botletics/SIM7000-LTE-Shield/Media/Adafruit IO Command Feed.PNG

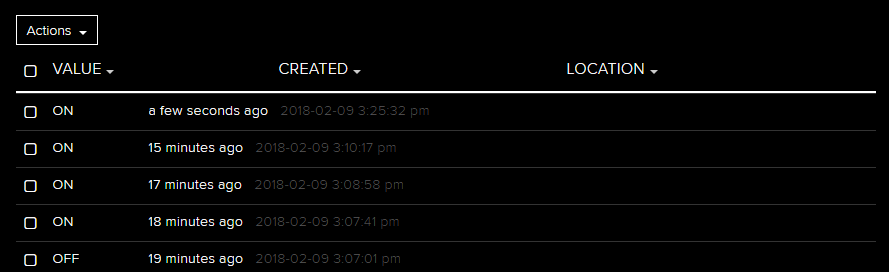
Media/Adafruit IO Command Feed.PNG
