botletics/SIM7000-LTE-Shield/Media/Adafruit IO Feeds.PNG

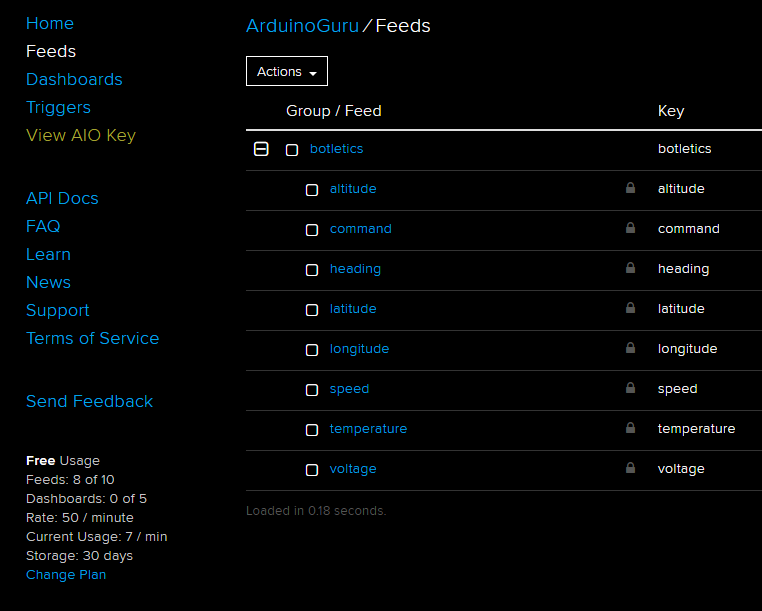
Media/Adafruit IO Feeds.PNG
