botletics/SIM7000-LTE-Shield/Media/AIO MQTT Command Message.PNG

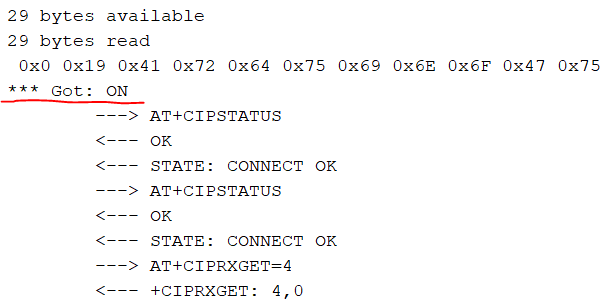
Media/AIO MQTT Command Message.PNG
