botletics/SIM7000-LTE-Shield/Media/Antenna Back.jpg

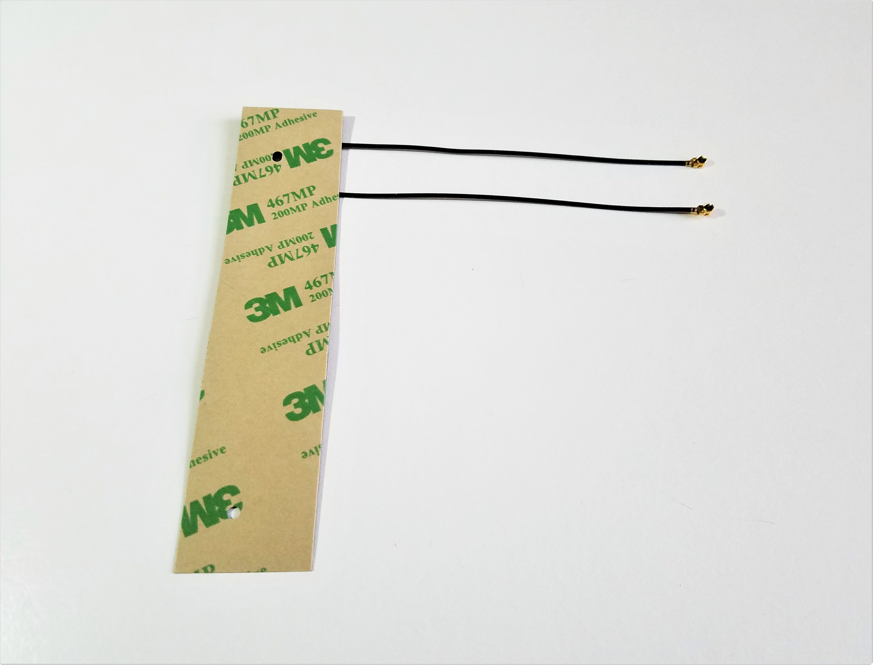
Media/Antenna Back.jpg
