botletics/SIM7000-LTE-Shield/Media/Antenna Front.jpg

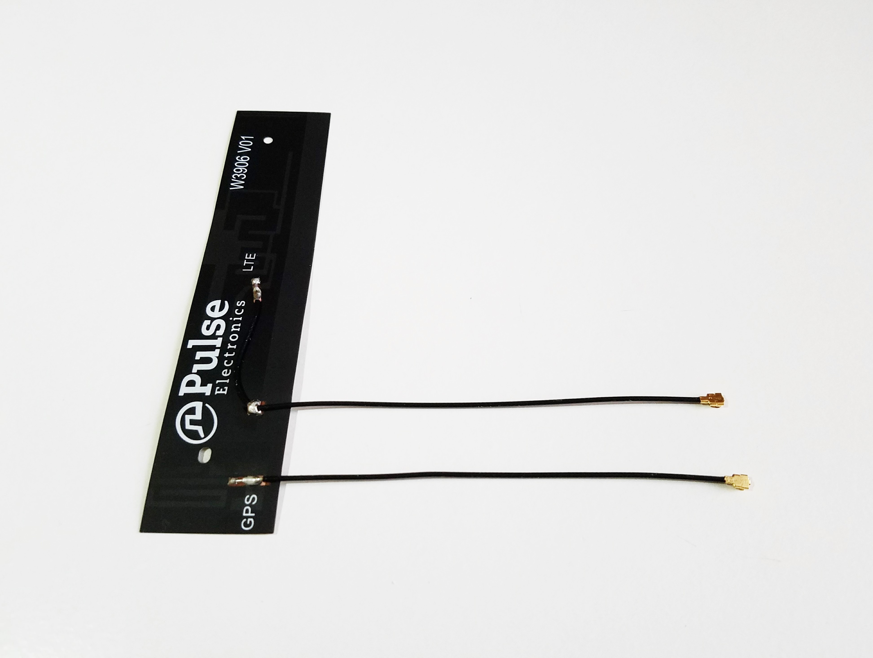
Media/Antenna Front.jpg
