botletics/SIM7000-LTE-Shield/Media/Arduino IDE Boards Screenshot.png

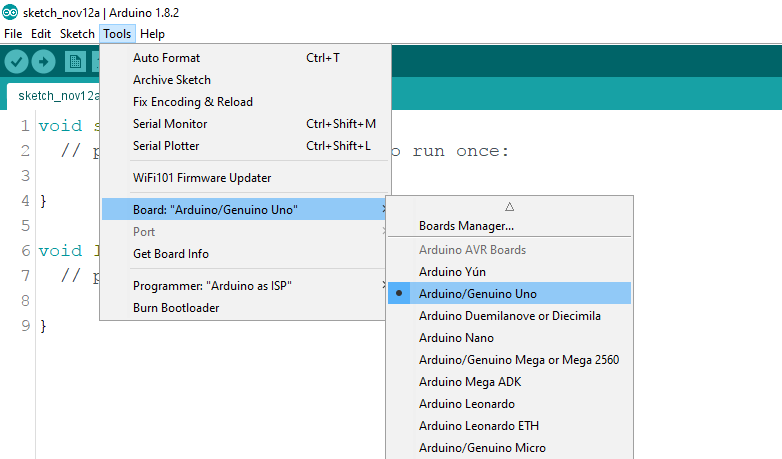
Media/Arduino IDE Boards Screenshot.png
