botletics/SIM7000-LTE-Shield/Media/Arduino IDE Example Screenshot.png

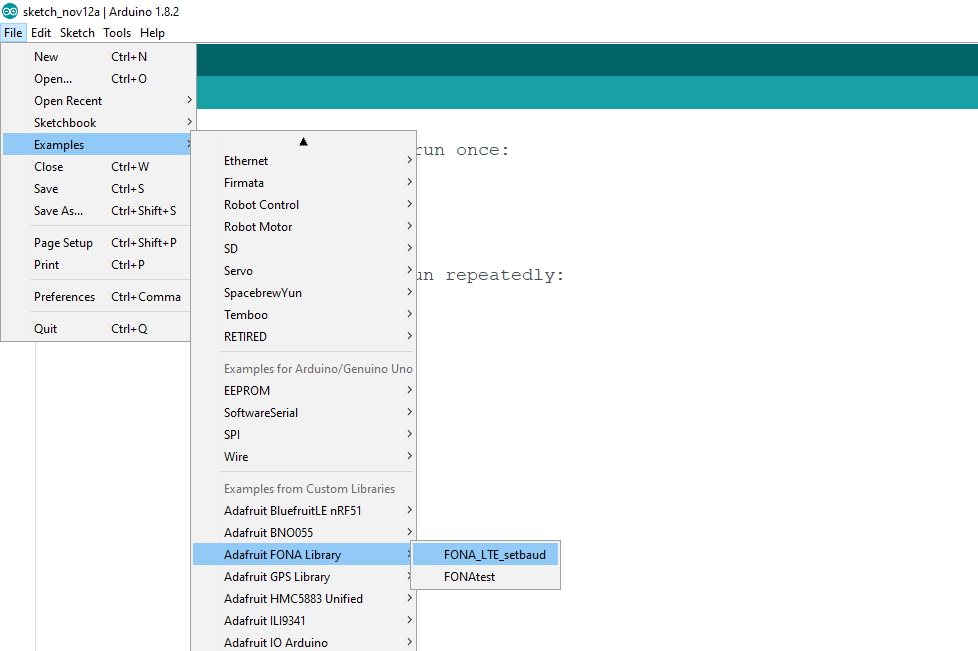
Media/Arduino IDE Example Screenshot.png
