botletics/SIM7000-LTE-Shield/Media/CAT-M_NB_Operator Map.jpg

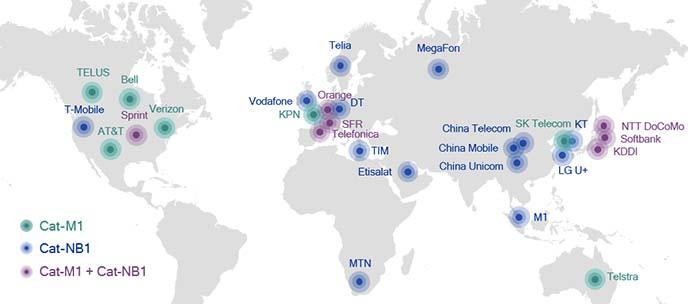
Media/CAT-M_NB_Operator Map.jpg
