botletics/SIM7000-LTE-Shield/Media/CloudMQTT Details Page.PNG

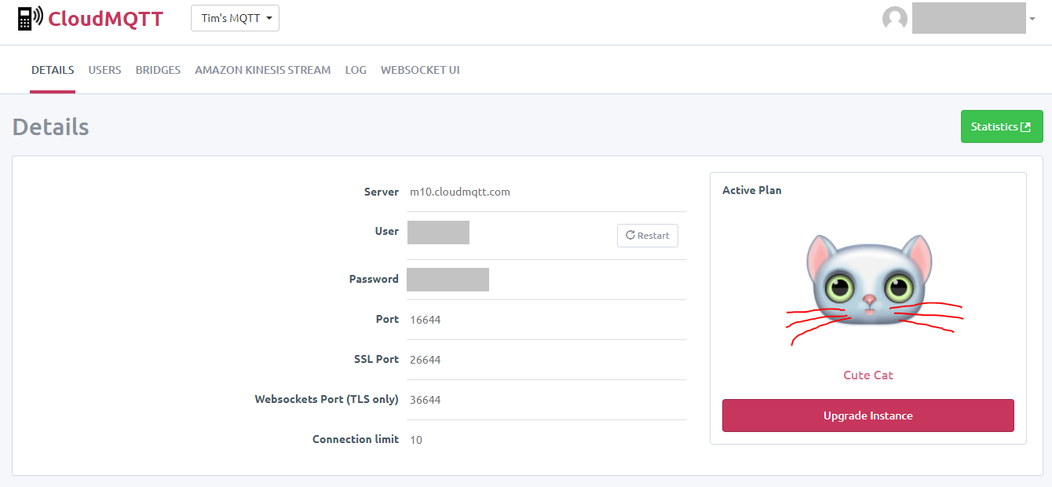
Media/CloudMQTT Details Page.PNG
