botletics/SIM7000-LTE-Shield/Media/CloudMQTT Websocket UI.PNG

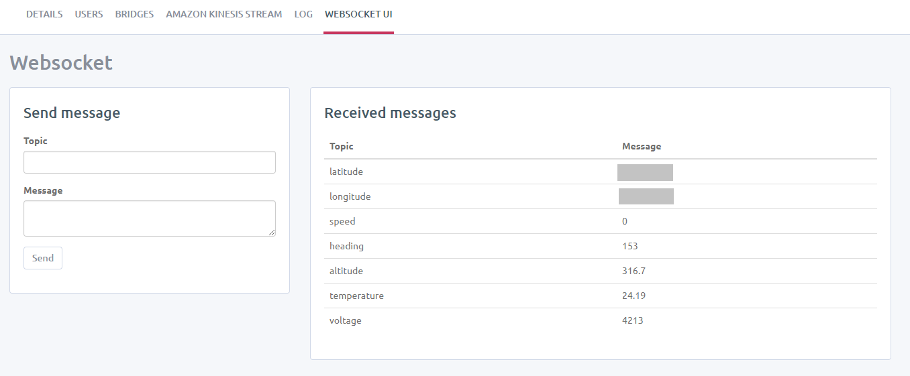
Media/CloudMQTT Websocket UI.PNG
