botletics/SIM7000-LTE-Shield/Media/Disable GPS.JPG

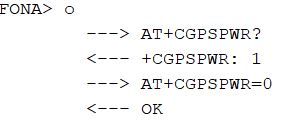
Media/Disable GPS.JPG
