botletics/SIM7000-LTE-Shield/Media/DONE LED Closeup v6.jpg

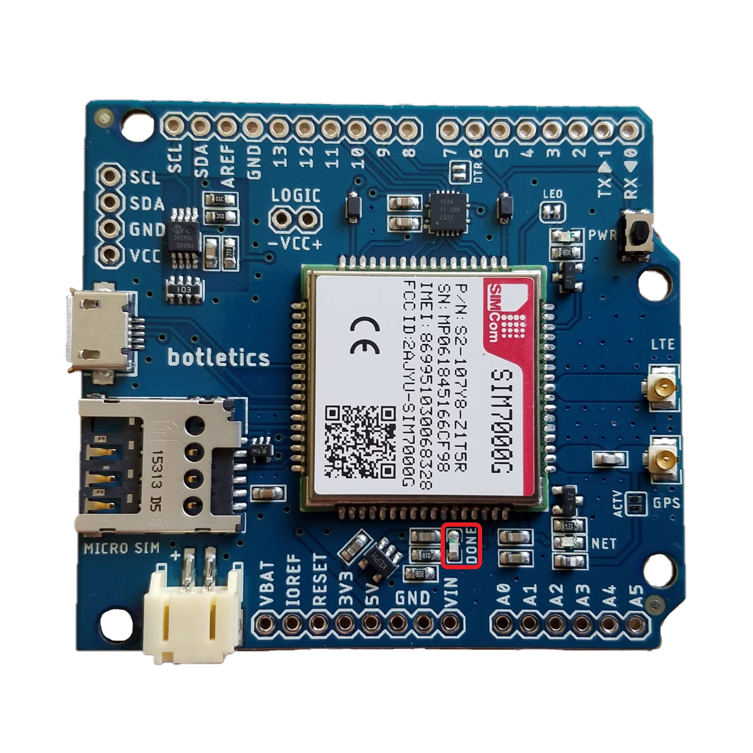
Media/DONE LED Closeup v6.jpg
