botletics/SIM7000-LTE-Shield/Media/Driver Update Remaining Updates.png

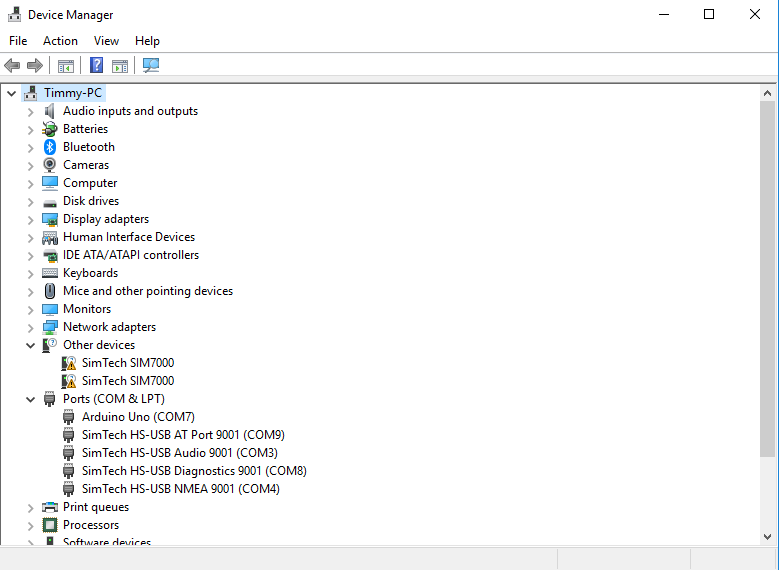
Media/Driver Update Remaining Updates.png
