botletics/SIM7000-LTE-Shield/Media/Driver Update Success COM Port.png

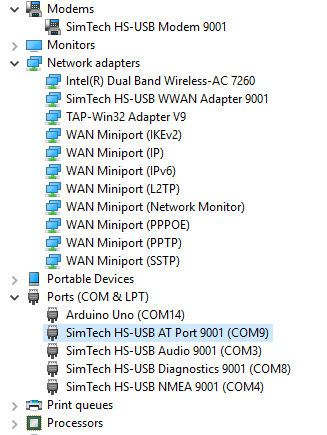
Media/Driver Update Success COM Port.png
