botletics/SIM7000-LTE-Shield/Media/Driver Update Success.png

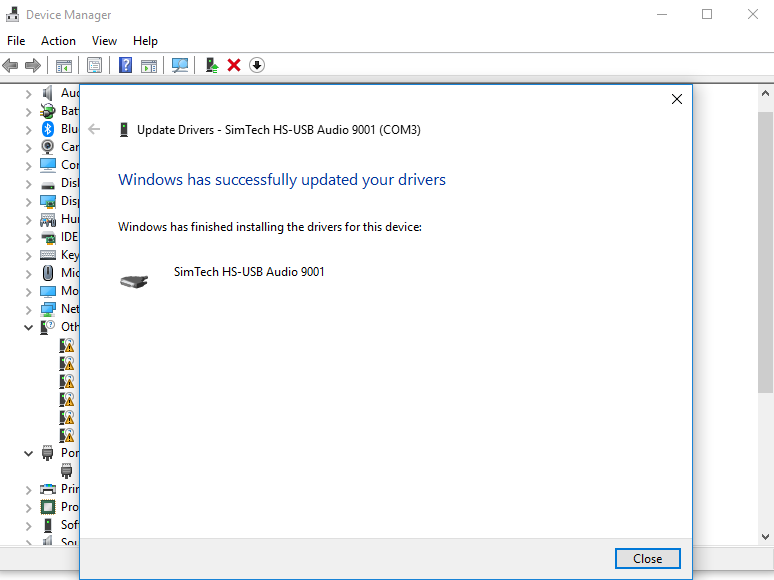
Media/Driver Update Success.png
