botletics/SIM7000-LTE-Shield/Media/Enable GPRS LTE.JPG

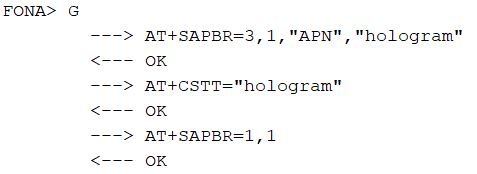
Media/Enable GPRS LTE.JPG
