botletics/SIM7000-LTE-Shield/Media/Enable GPRS.JPG

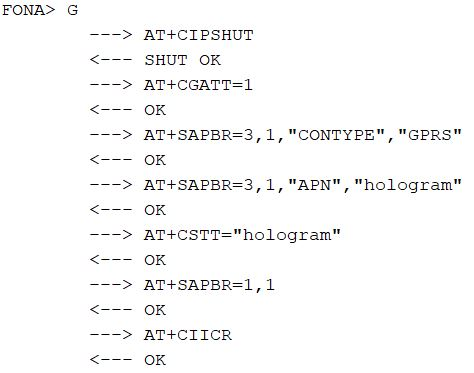
Media/Enable GPRS.JPG
