botletics/SIM7000-LTE-Shield/Media/Enable GPS.JPG

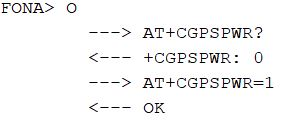
Media/Enable GPS.JPG
