botletics/SIM7000-LTE-Shield/Media/Folder Screenshot 1.png

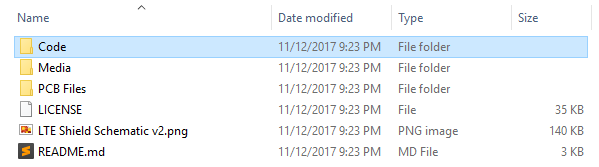
Media/Folder Screenshot 1.png
