botletics/SIM7000-LTE-Shield/Media/Folder Screenshot 2.png

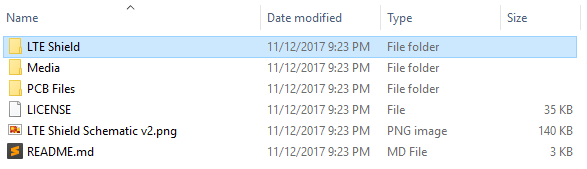
Media/Folder Screenshot 2.png
