botletics/SIM7000-LTE-Shield/Media/FONAtest Batt Example.PNG

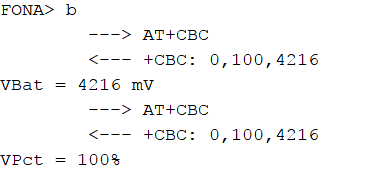
Media/FONAtest Batt Example.PNG
