botletics/SIM7000-LTE-Shield/Media/Github Download ZIP.png

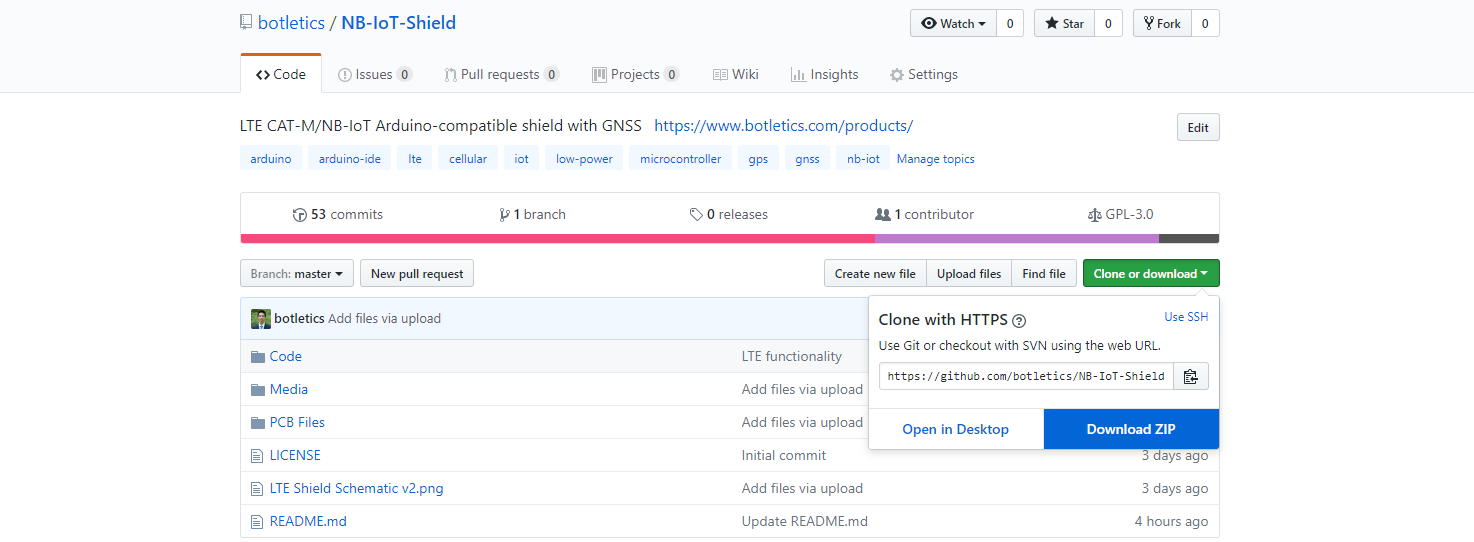
Media/Github Download ZIP.png
