botletics/SIM7000-LTE-Shield/Media/Hologram Console Data.PNG

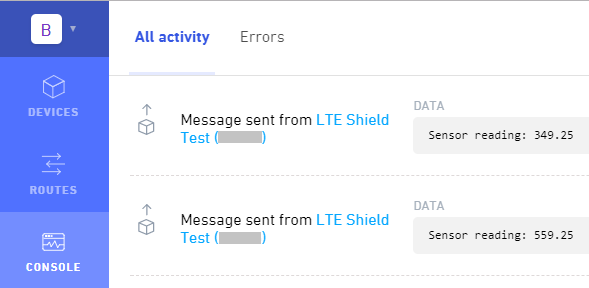
Media/Hologram Console Data.PNG
