botletics/SIM7000-LTE-Shield/Media/Hologram Device Screen.png

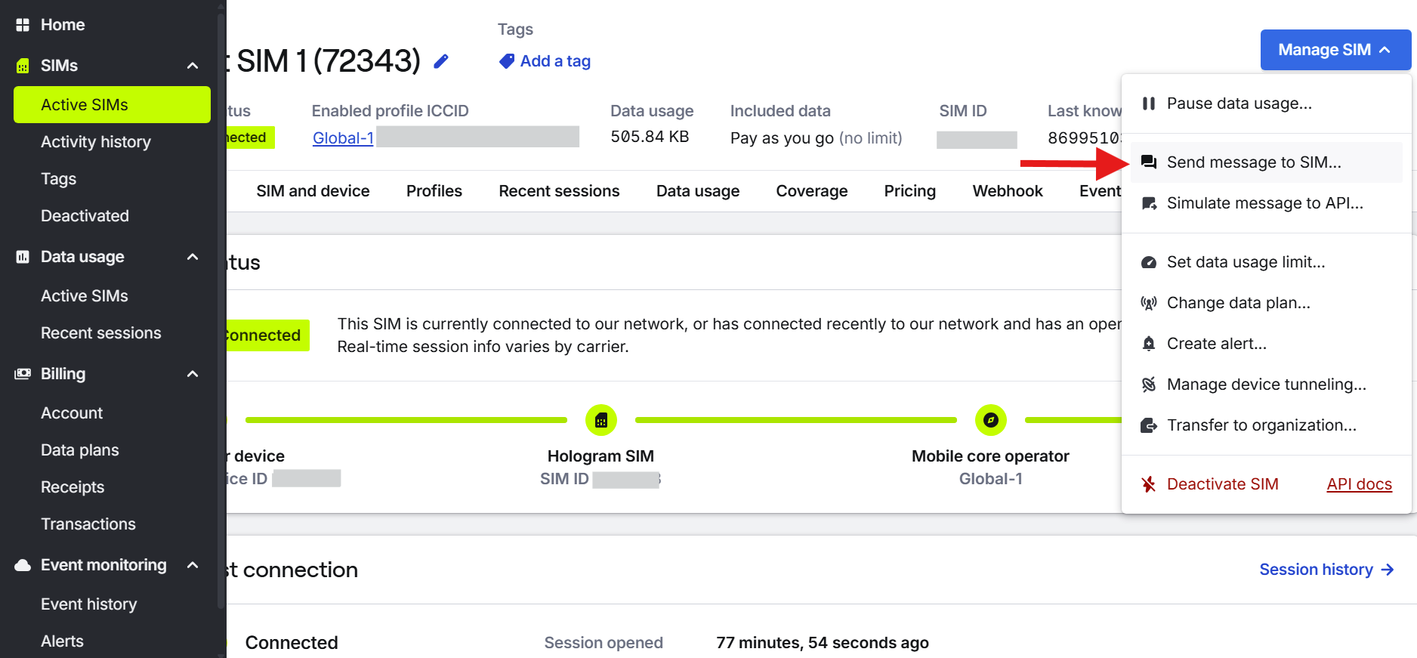
Media/Hologram Device Screen.png
