botletics/SIM7000-LTE-Shield/Media/Hologram Route Email Example.PNG

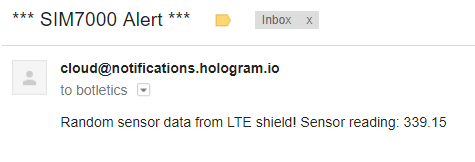
Media/Hologram Route Email Example.PNG
