botletics/SIM7000-LTE-Shield/Media/Hologram Route Email Fields.PNG

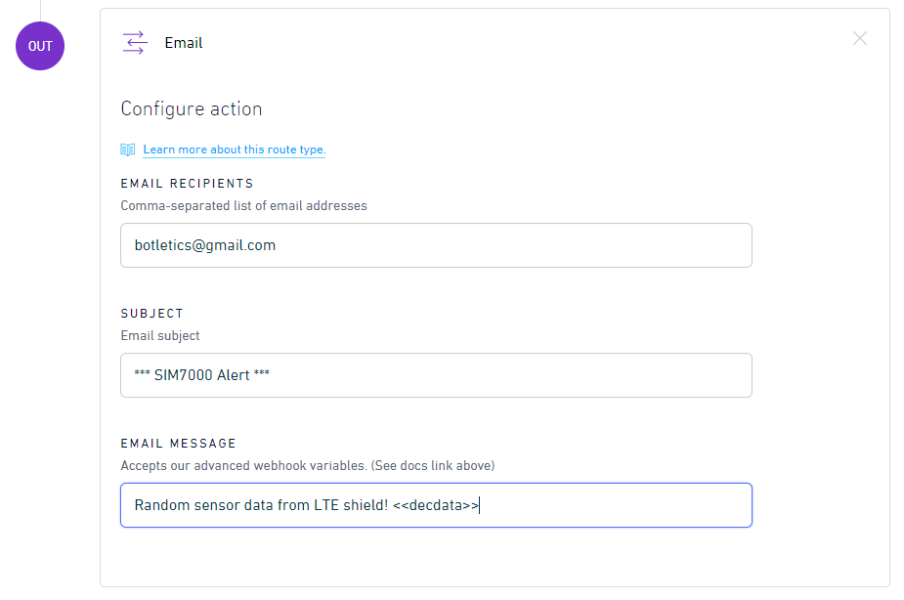
Media/Hologram Route Email Fields.PNG
