botletics/SIM7000-LTE-Shield/Media/Hologram Route SMS Action.PNG

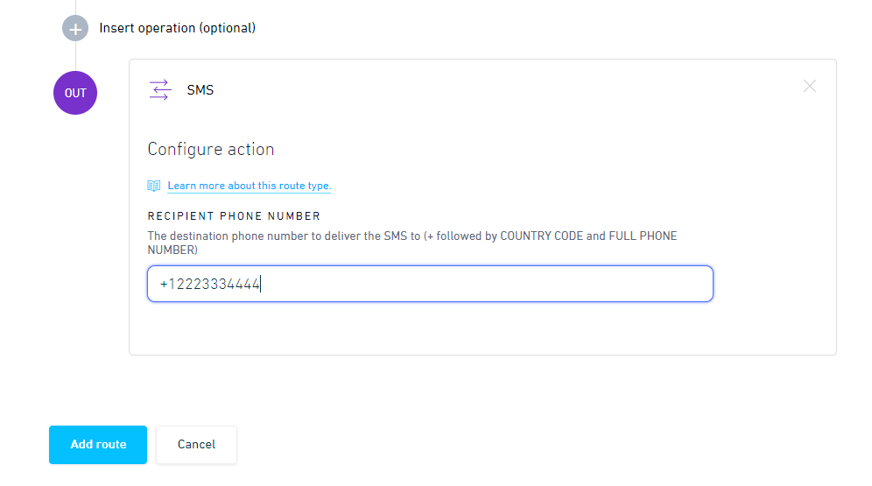
Media/Hologram Route SMS Action.PNG
