botletics/SIM7000-LTE-Shield/Media/Hologram Route SMS Topic.PNG

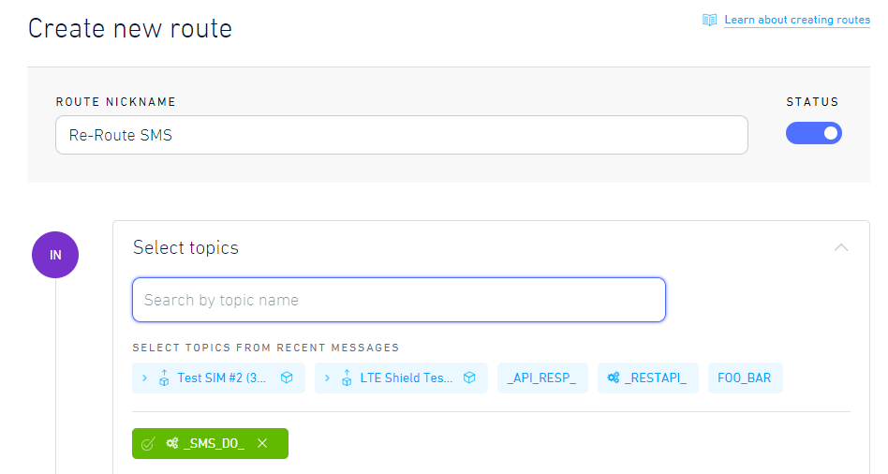
Media/Hologram Route SMS Topic.PNG
