botletics/SIM7000-LTE-Shield/Media/IoT Example GET Request.PNG

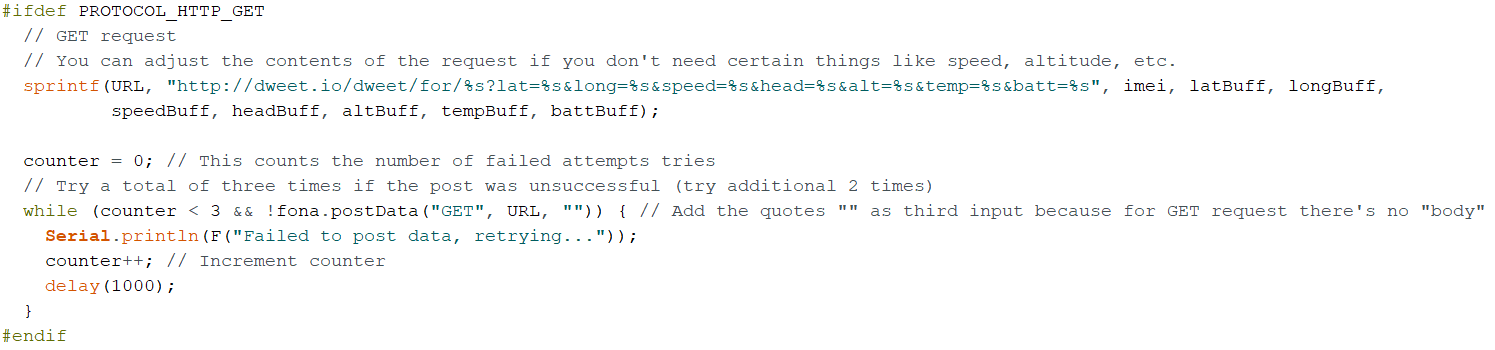
Media/IoT Example GET Request.PNG
