botletics/SIM7000-LTE-Shield/Media/IoT Example MQTT Publish Feeds.PNG

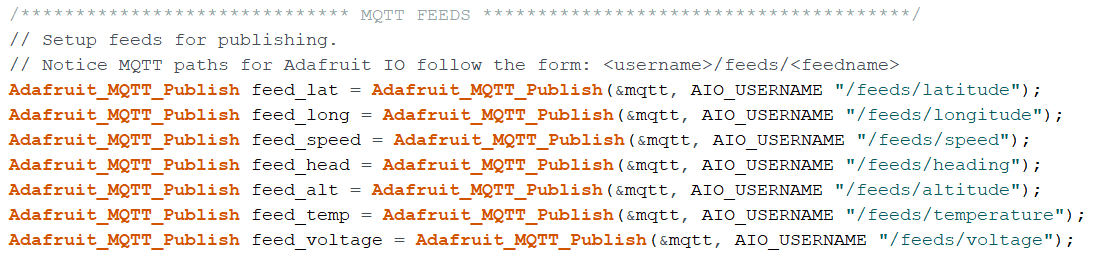
Media/IoT Example MQTT Publish Feeds.PNG
