botletics/SIM7000-LTE-Shield/Media/IoT Example POST Request.PNG

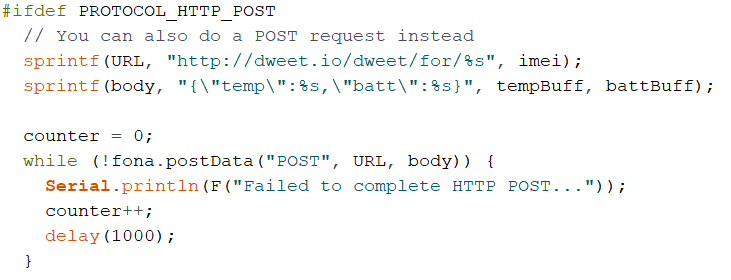
Media/IoT Example POST Request.PNG
