botletics/SIM7000-LTE-Shield/Media/IoT Example Sampling Rate.PNG

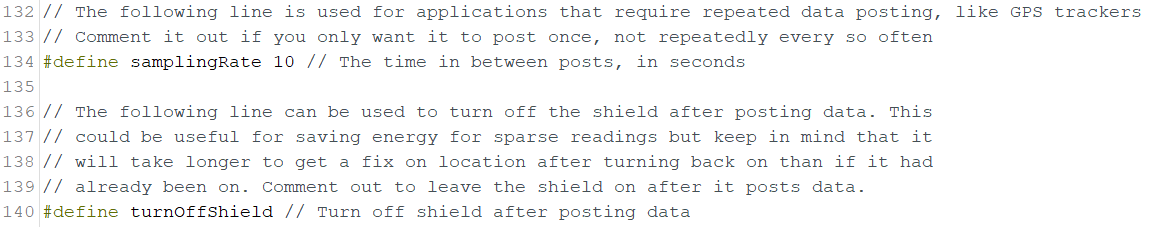
Media/IoT Example Sampling Rate.PNG
