botletics/SIM7000-LTE-Shield/Media/ITU Regions.png

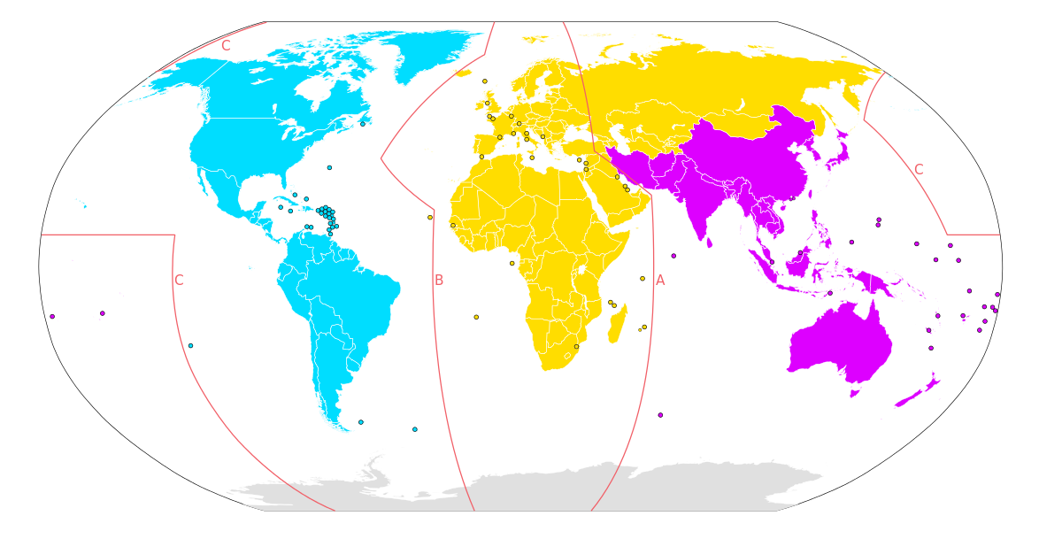
Media/ITU Regions.png
