botletics/SIM7000-LTE-Shield/Media/JST Connector Closeup v6.jpg

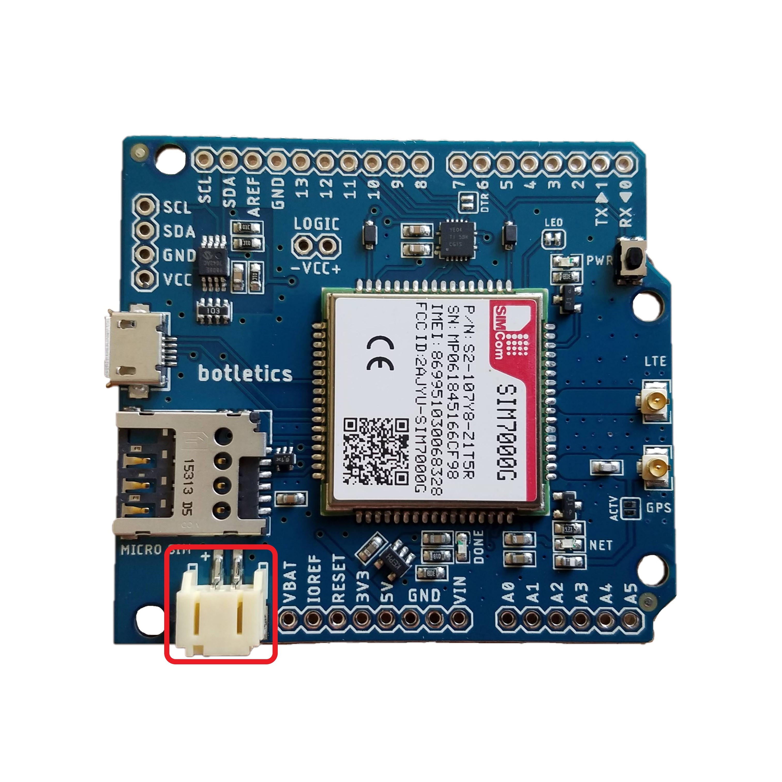
Media/JST Connector Closeup v6.jpg
