botletics/SIM7000-LTE-Shield/Media/Logic Voltage Selection Jumper.PNG

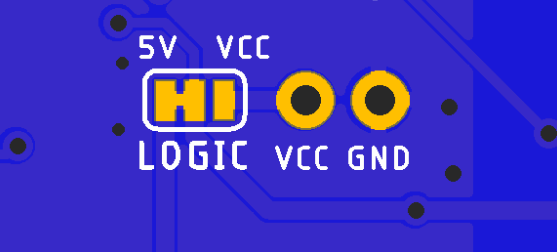
Media/Logic Voltage Selection Jumper.PNG
