botletics/SIM7000-LTE-Shield/Media/LTE Bands.JPG

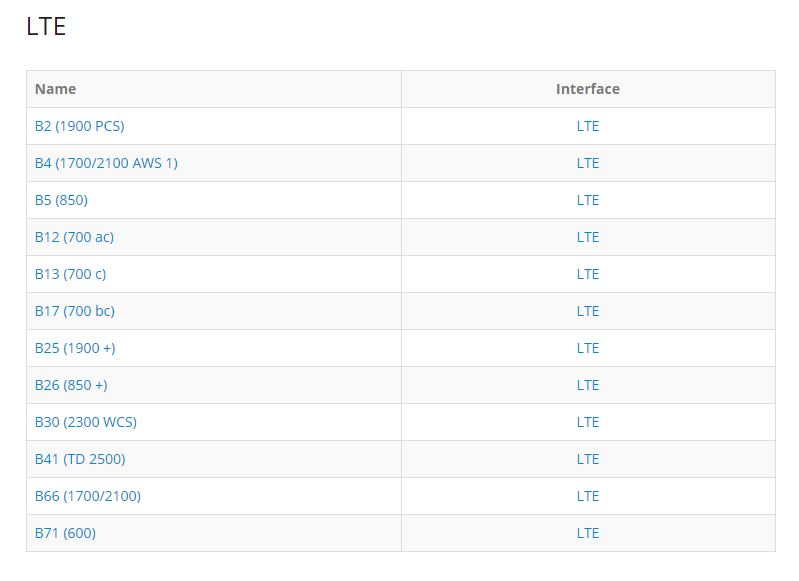
Media/LTE Bands.JPG
