botletics/SIM7000-LTE-Shield/Media/MCP9098 Demo.PNG

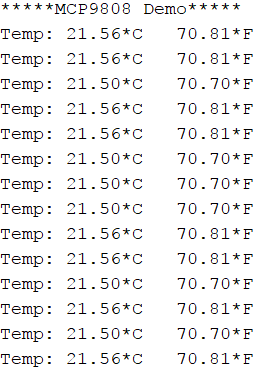
Media/MCP9098 Demo.PNG
