botletics/SIM7000-LTE-Shield/Media/MCP9808 Example Screenshot.png

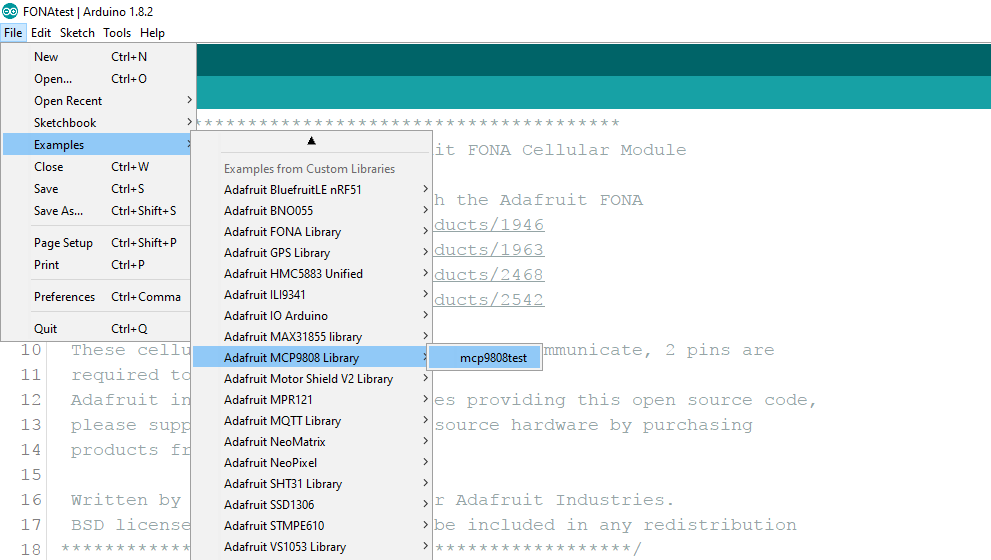
Media/MCP9808 Example Screenshot.png
