botletics/SIM7000-LTE-Shield/Media/Open Sesame from Hologram.png

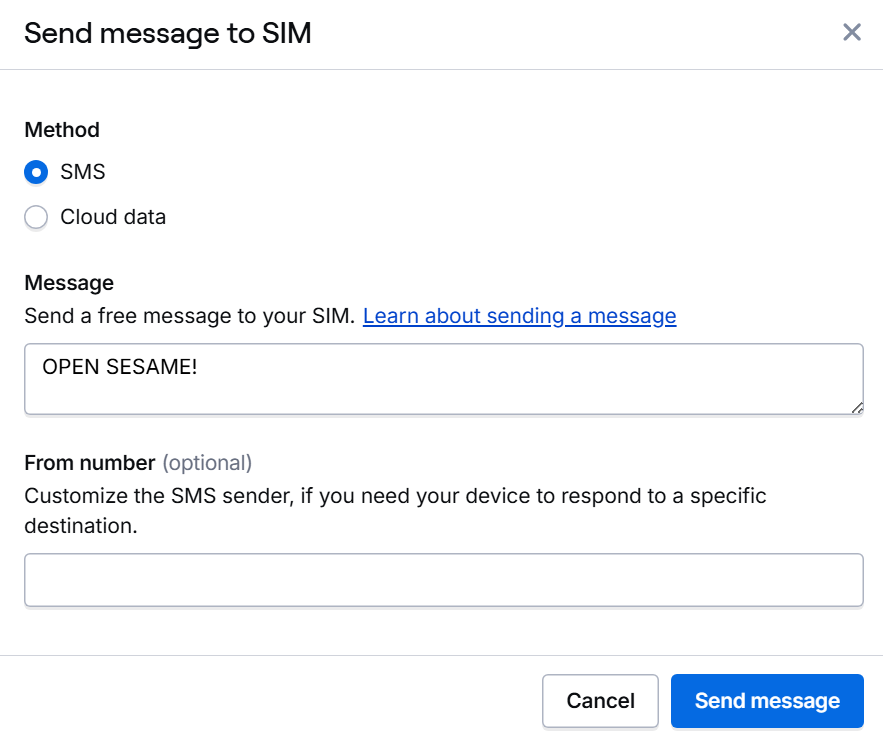
Media/Open Sesame from Hologram.png
