botletics/SIM7000-LTE-Shield/Media/QDL Tool Windows Compatibility Prompt.PNG

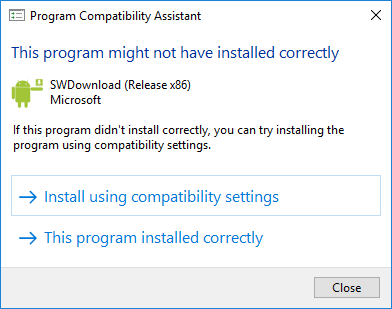
Media/QDL Tool Windows Compatibility Prompt.PNG
