botletics/SIM7000-LTE-Shield/Media/Read Dweet.JPG

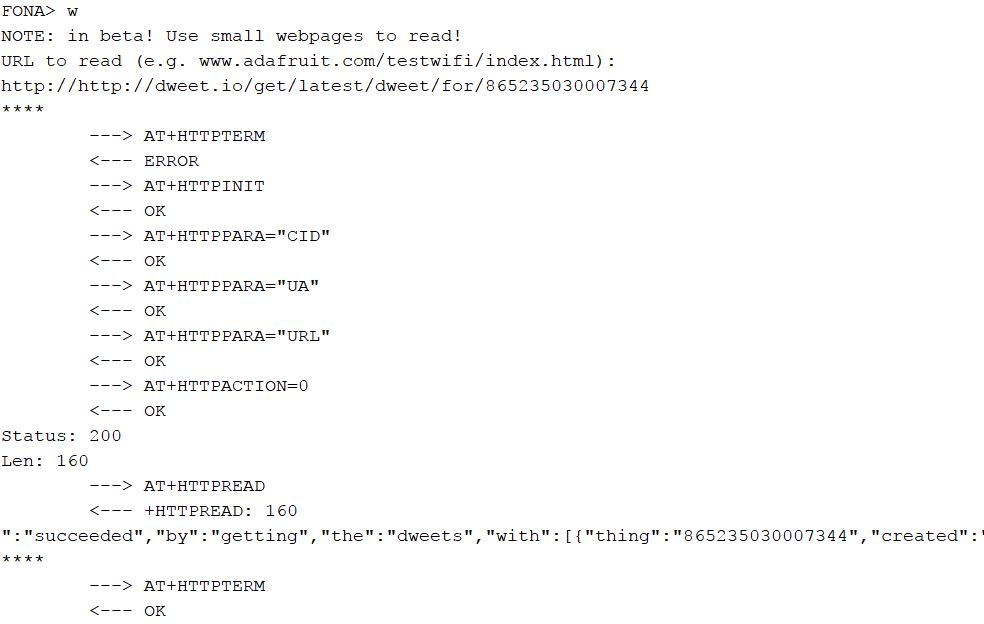
Media/Read Dweet.JPG
