botletics/SIM7000-LTE-Shield/Media/Read Webpage.JPG

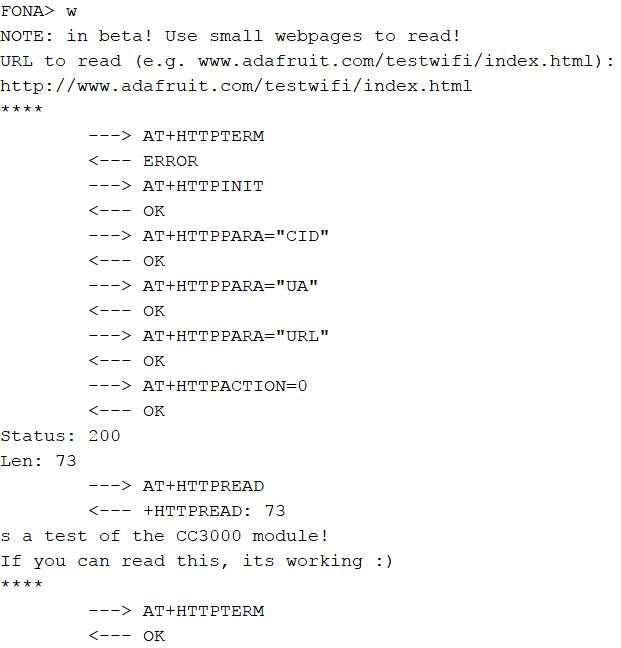
Media/Read Webpage.JPG
