botletics/SIM7000-LTE-Shield/Media/Send SMS from Hologram 1.png

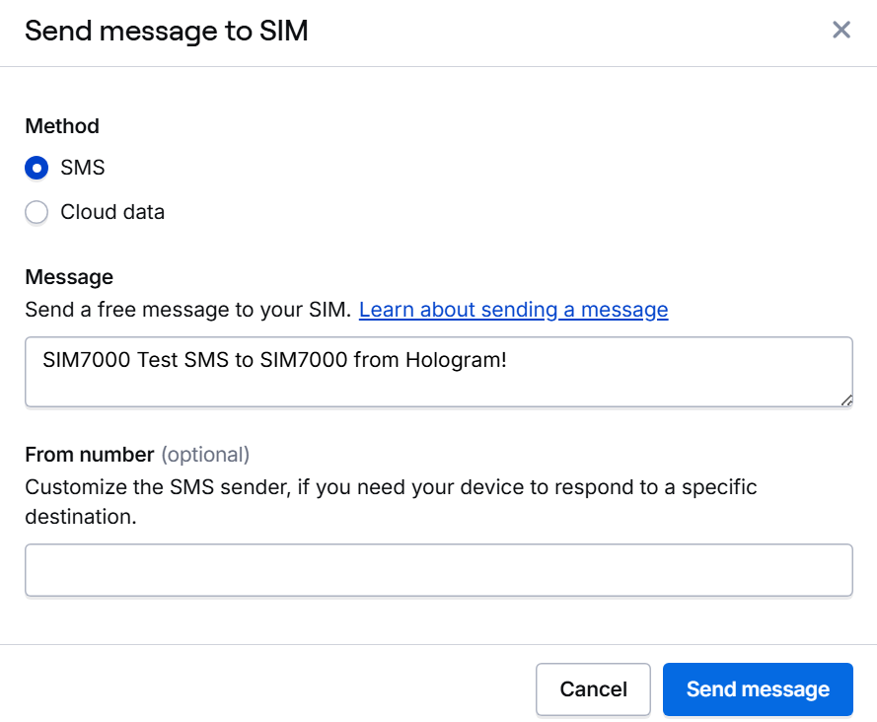
Media/Send SMS from Hologram 1.png
