botletics/SIM7000-LTE-Shield/Media/Send SMS from Hologram.png

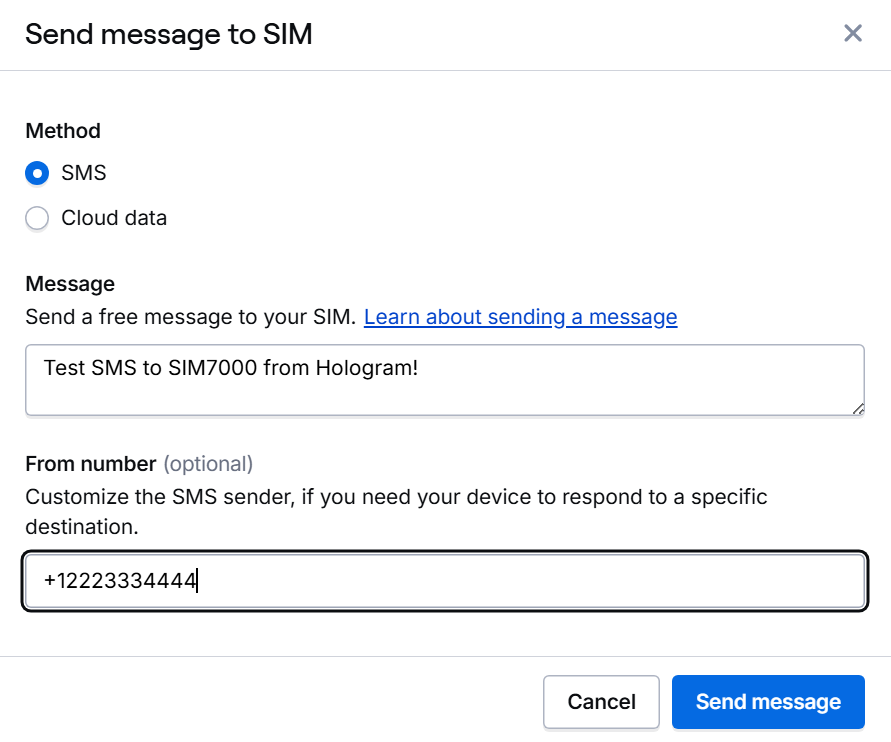
Media/Send SMS from Hologram.png
