botletics/SIM7000-LTE-Shield/Media/Send SMS.png

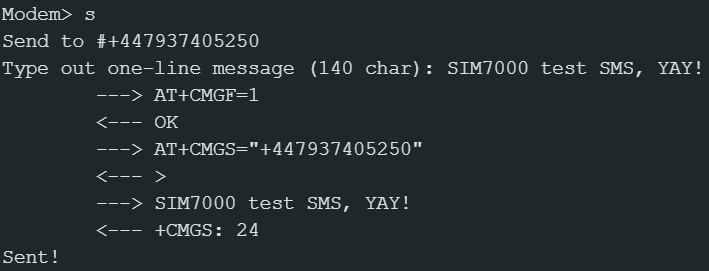
Media/Send SMS.png
