botletics/SIM7000-LTE-Shield/Media/Send to Dweet.JPG

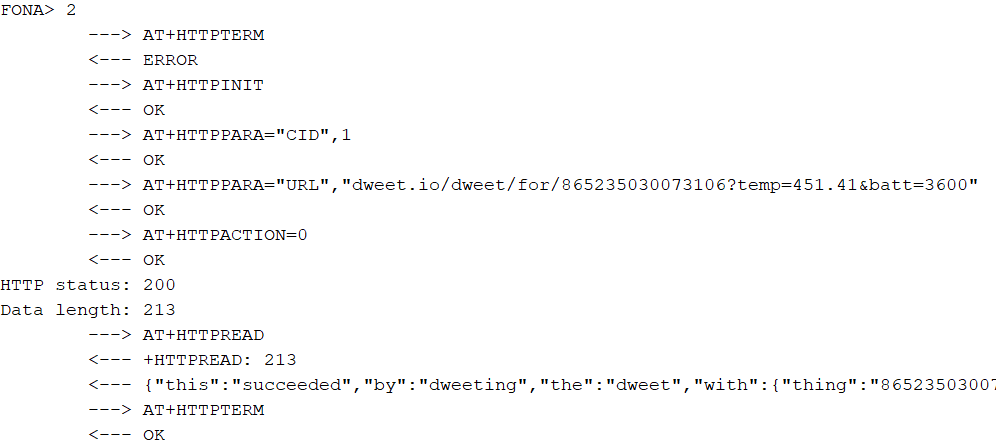
Media/Send to Dweet.JPG
