botletics/SIM7000-LTE-Shield/Media/SIM7000 Drivers Device Manager.JPG

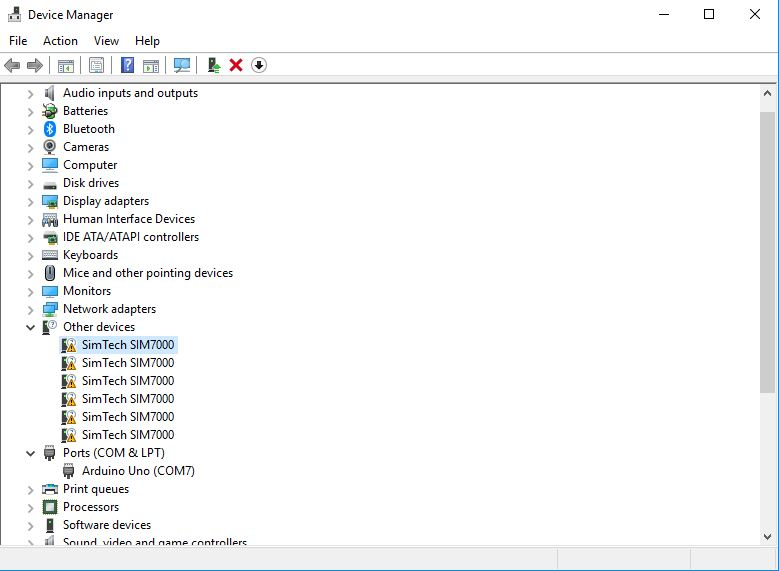
Media/SIM7000 Drivers Device Manager.JPG
