botletics/SIM7000-LTE-Shield/Media/SIM7000 LTE_Demo Serial Monitor 1.PNG

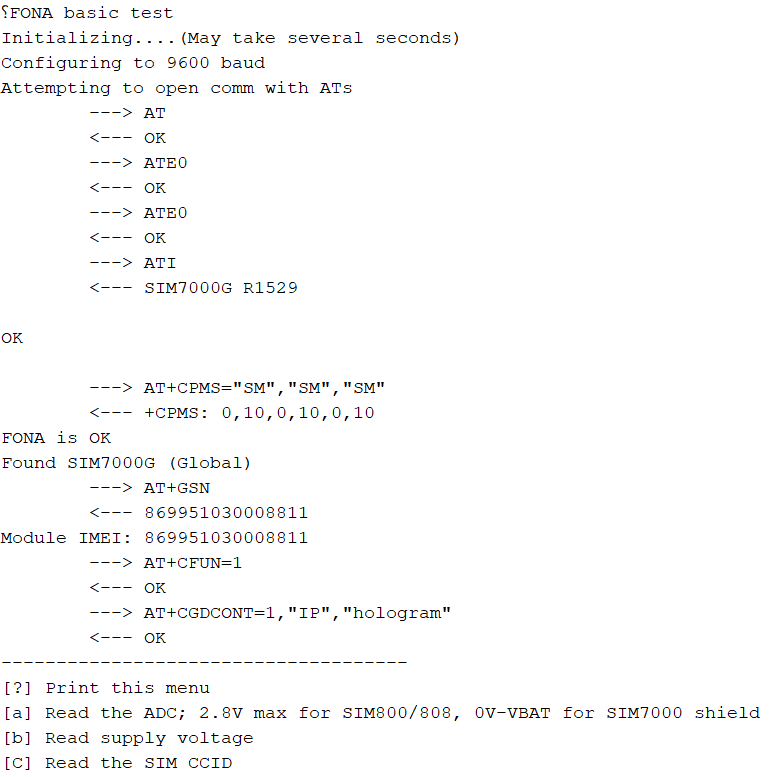
Media/SIM7000 LTE_Demo Serial Monitor 1.PNG
