botletics/SIM7000-LTE-Shield/Media/SIM7000 LTE_Demo Serial Tunnel.PNG

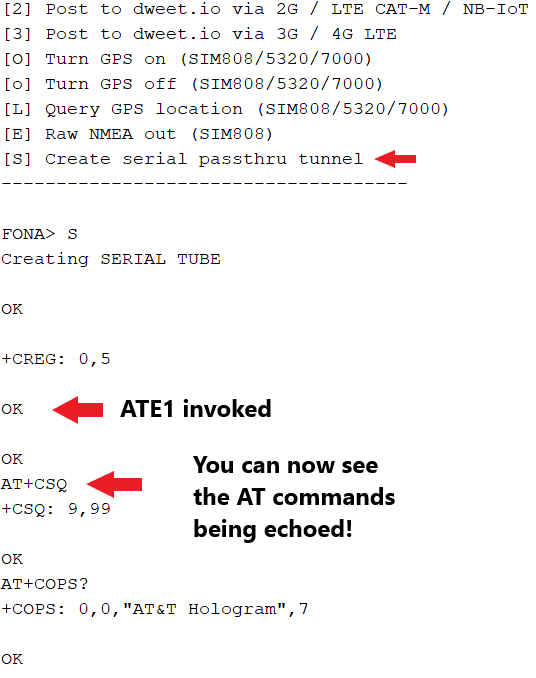
Media/SIM7000 LTE_Demo Serial Tunnel.PNG
