botletics/SIM7000-LTE-Shield/Media/SIM7000 Shield Annotated Diagram Production v5.jpg

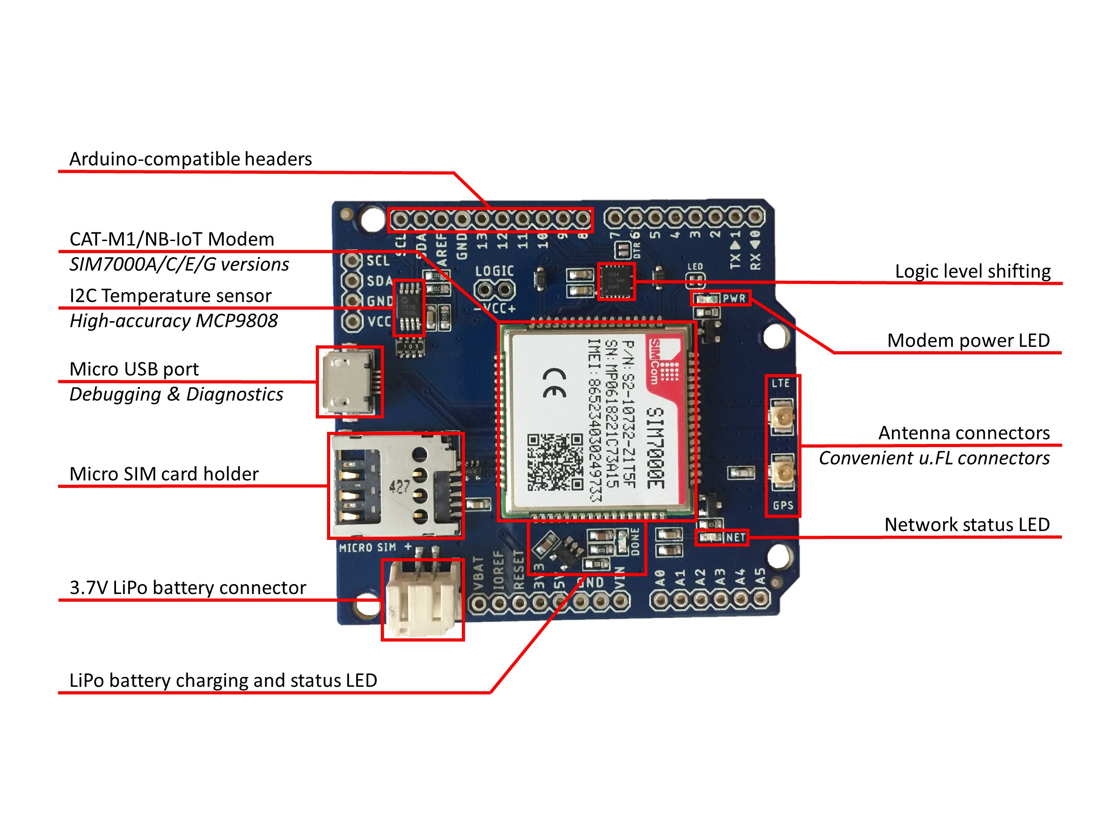
Media/SIM7000 Shield Annotated Diagram Production v5.jpg
