botletics/SIM7000-LTE-Shield/Media/SIM7000 Shield on Arduino Uno v5.jpg

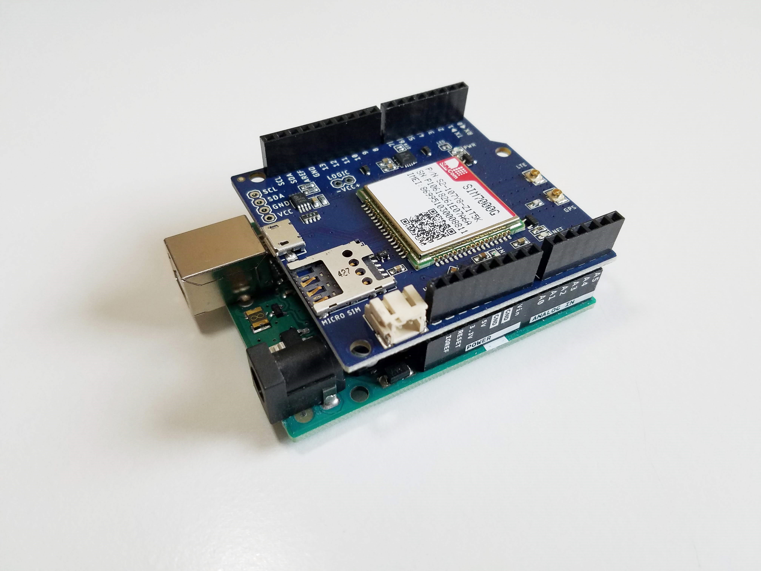
Media/SIM7000 Shield on Arduino Uno v5.jpg
