botletics/SIM7000-LTE-Shield/Media/SIM7000 Shield v5 Back with Headers.jpg

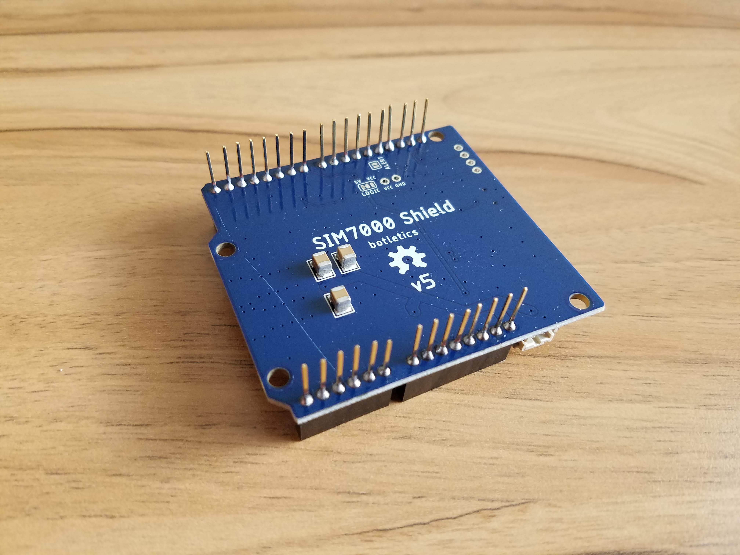
Media/SIM7000 Shield v5 Back with Headers.jpg
