botletics/SIM7000-LTE-Shield/Media/SIM7000 Shield v6 Back Cover Photo.jpg

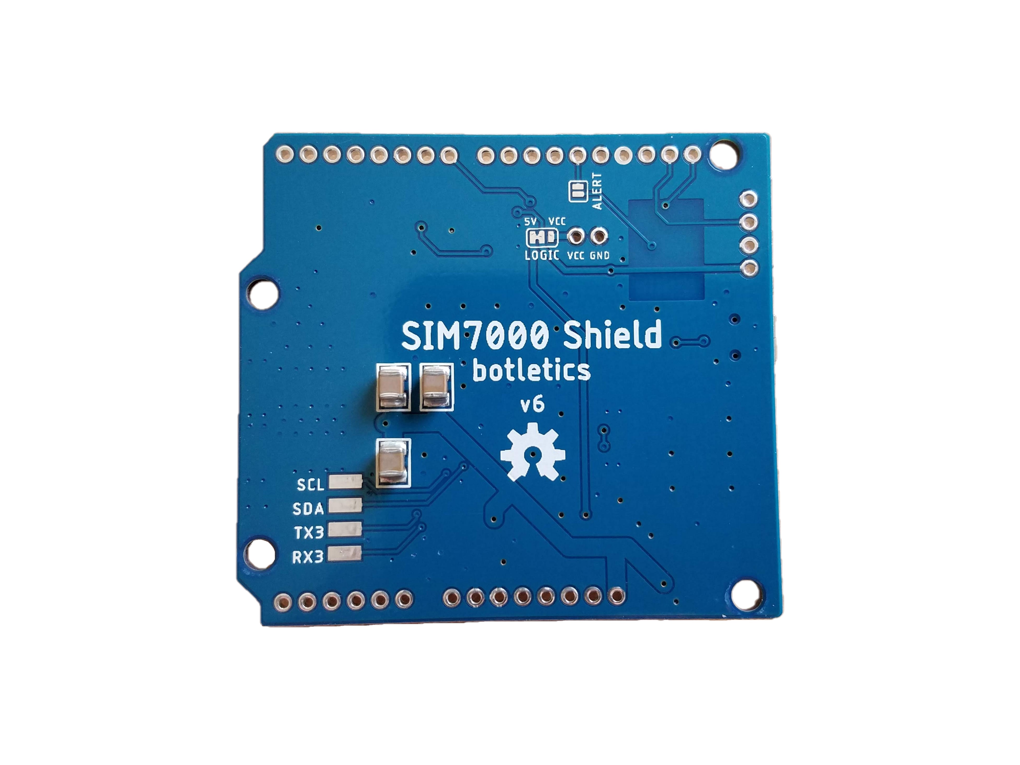
Media/SIM7000 Shield v6 Back Cover Photo.jpg
