botletics/SIM7000-LTE-Shield/Media/SIM7000 v6 Kit.jpg

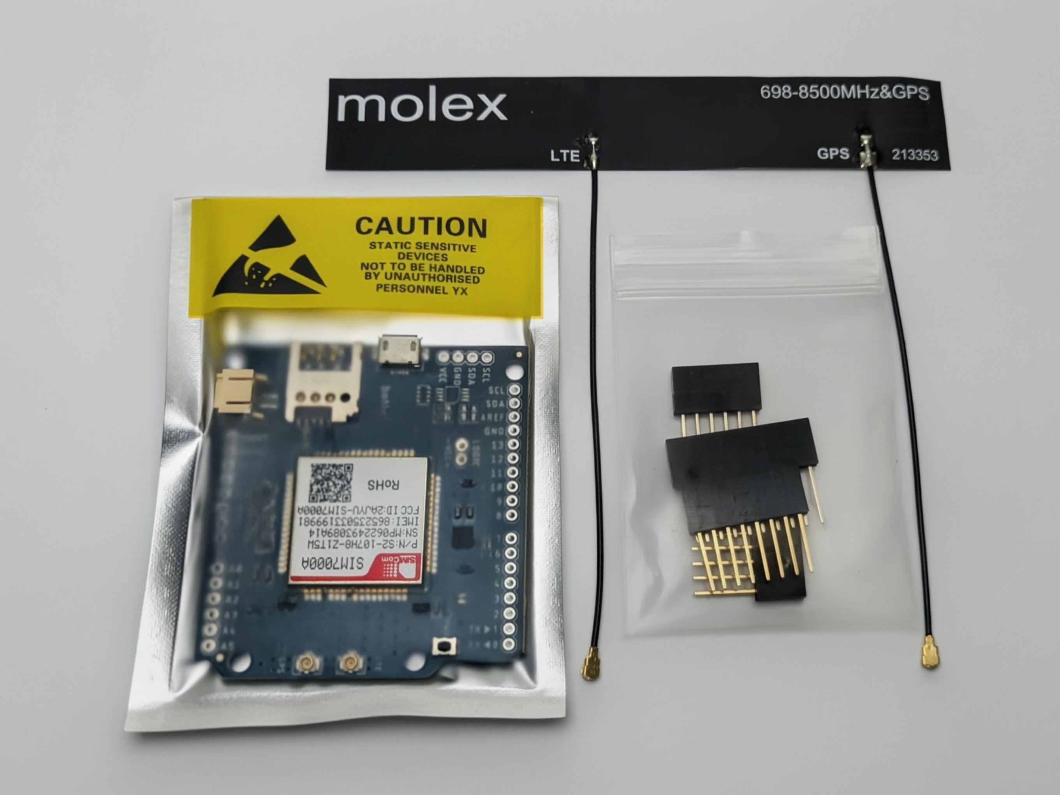
Media/SIM7000 v6 Kit.jpg
