botletics/SIM7000-LTE-Shield/Media/SIM7000G on Arduino.jpg

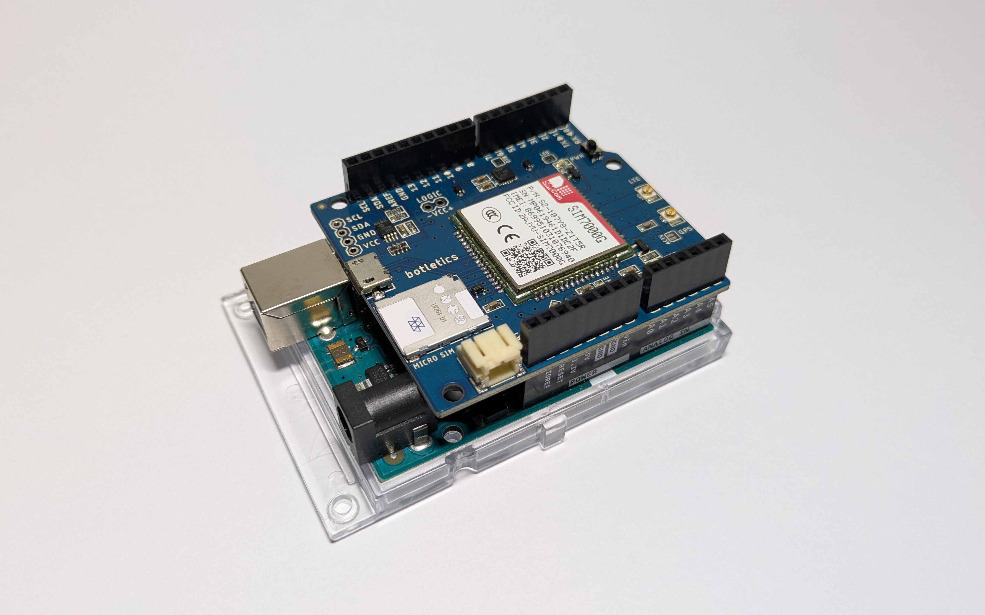
Media/SIM7000G on Arduino.jpg
