botletics/SIM7000-LTE-Shield/Media/SIM Card Insertion v6.jpg

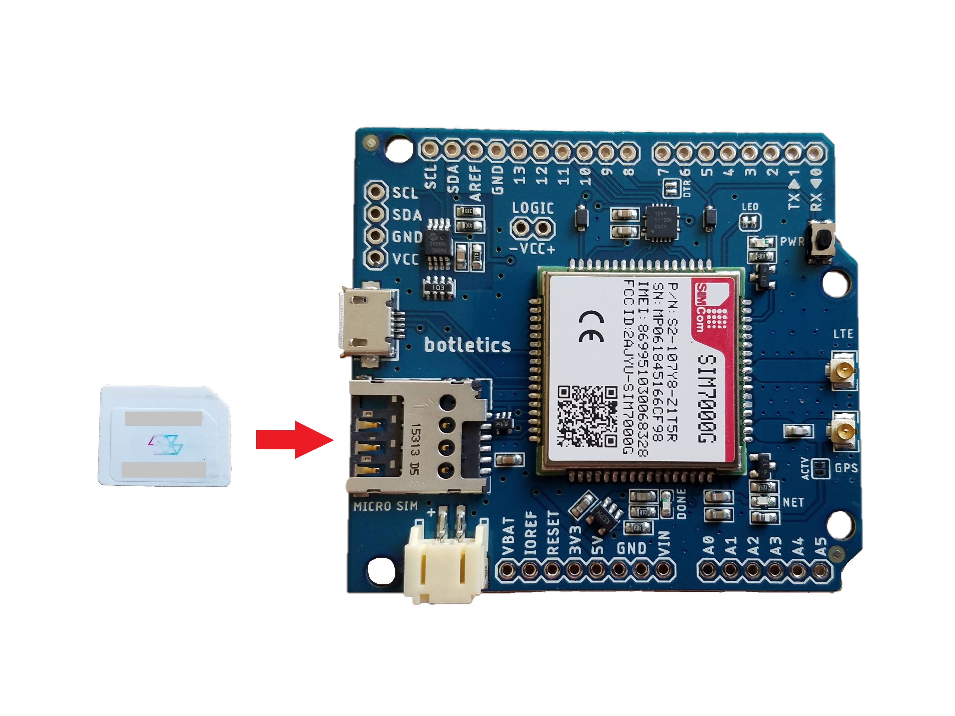
Media/SIM Card Insertion v6.jpg
