botletics/SIM7000-LTE-Shield/Media/SMS_Response Log.png

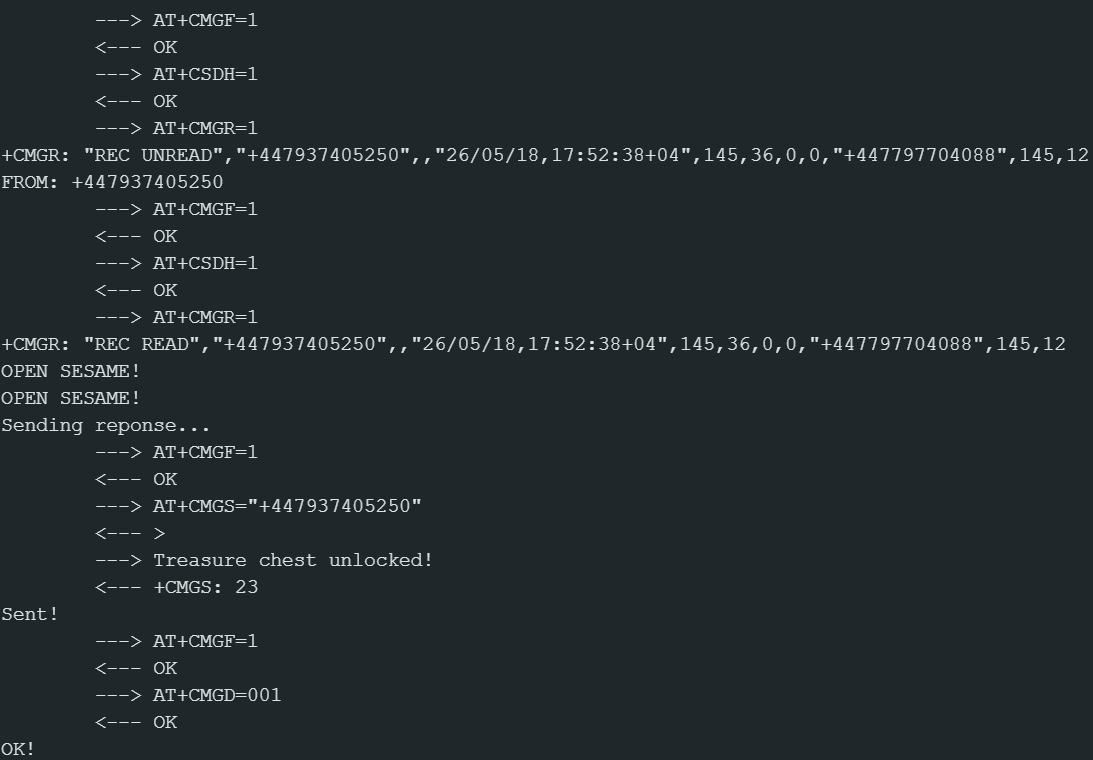
Media/SMS_Response Log.png
