botletics/SIM7000-LTE-Shield/Media/Update Driver.png

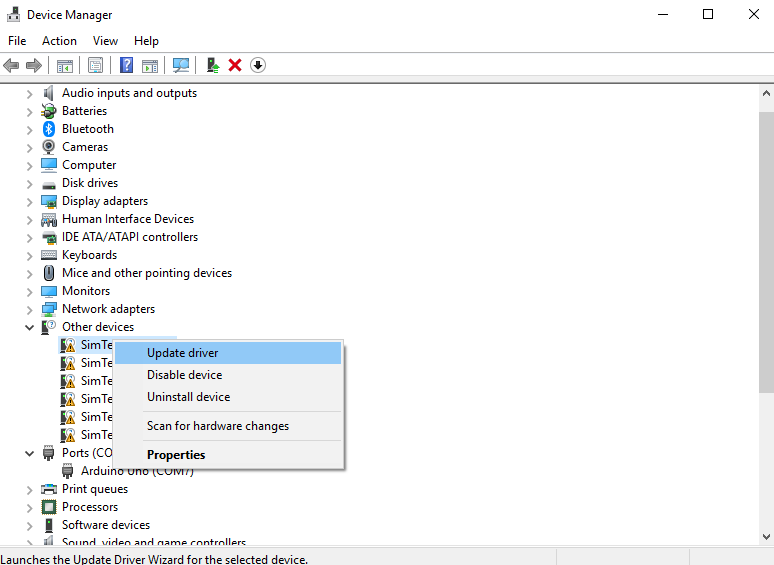
Media/Update Driver.png
