botletics/SIM7000-LTE-Shield/Media/USB AT Commands Putty.PNG

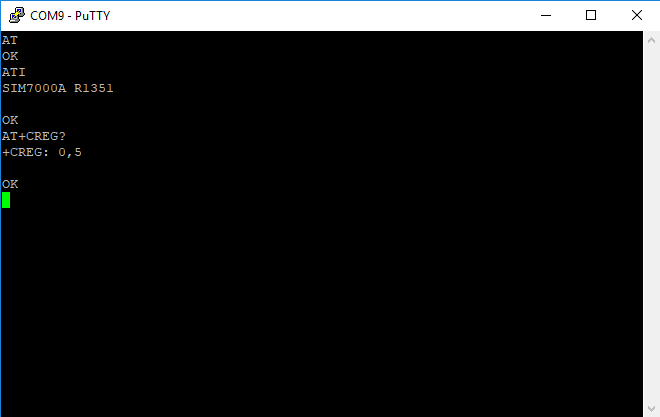
Media/USB AT Commands Putty.PNG
