botletics/SIM7000-LTE-Shield/Schematics/SIM7000 Shield Schematic v5.png

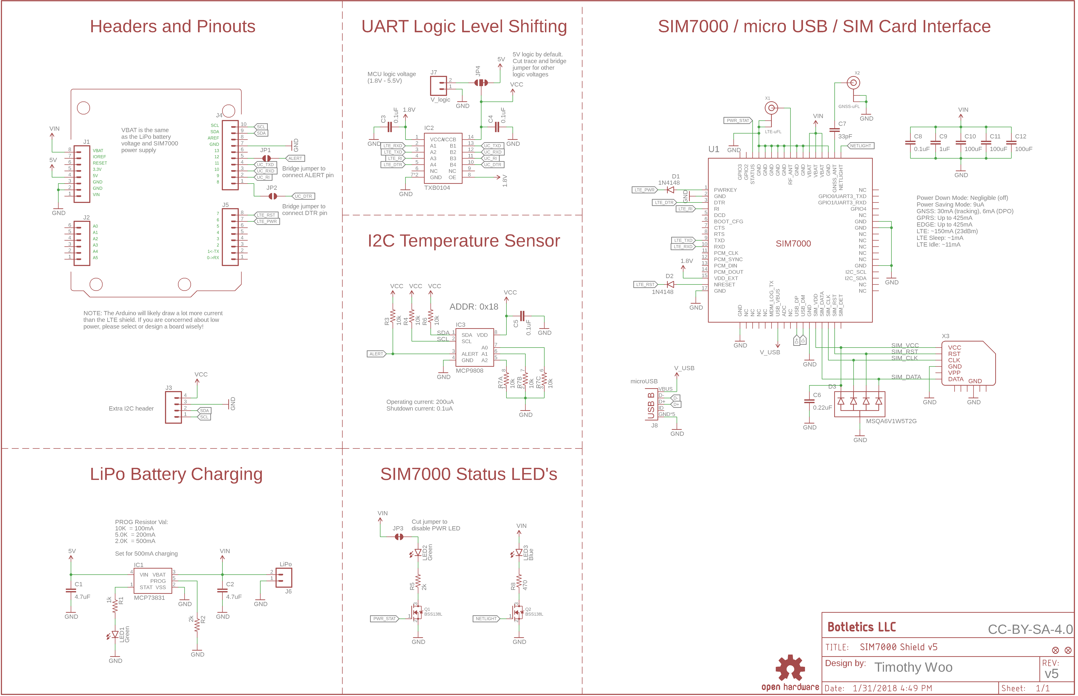
Schematics/SIM7000 Shield Schematic v5.png
