botletics/SIM7000-LTE-Shield/Media/SIM7000G Parts Needed.jpg

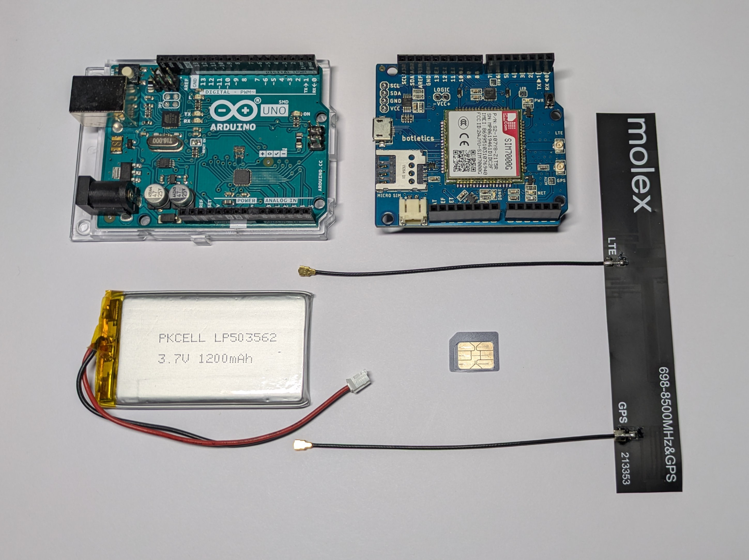
Media/SIM7000G Parts Needed.jpg
