botletics/SIM7000-LTE-Shield/Media/Arduino Assembly with Cable v5.jpg

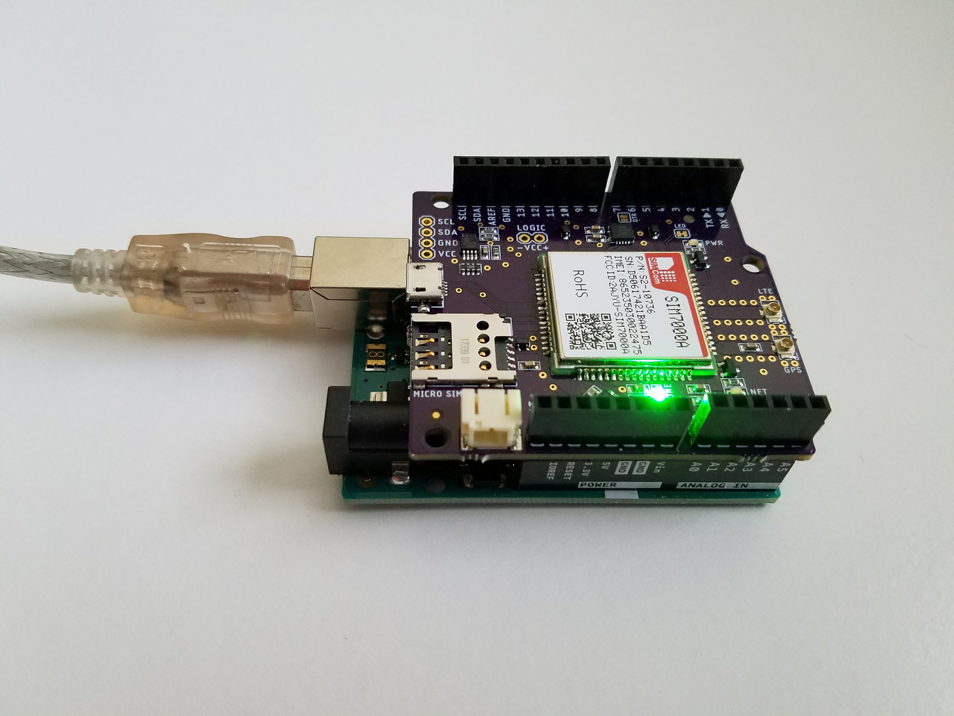
Media/Arduino Assembly with Cable v5.jpg
