botletics/SIM7000-LTE-Shield/Media/IoT Example CloudMQTT Setup.PNG

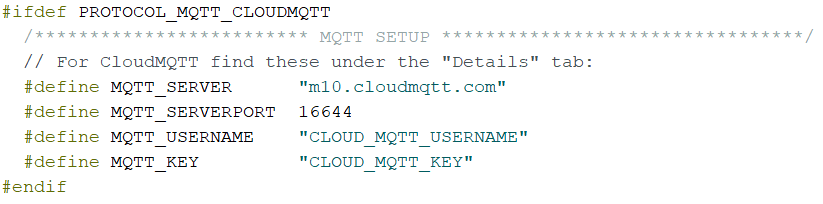
Media/IoT Example CloudMQTT Setup.PNG
