botletics/SIM7000-LTE-Shield/Media/SIM7000G Complete Setup.jpg

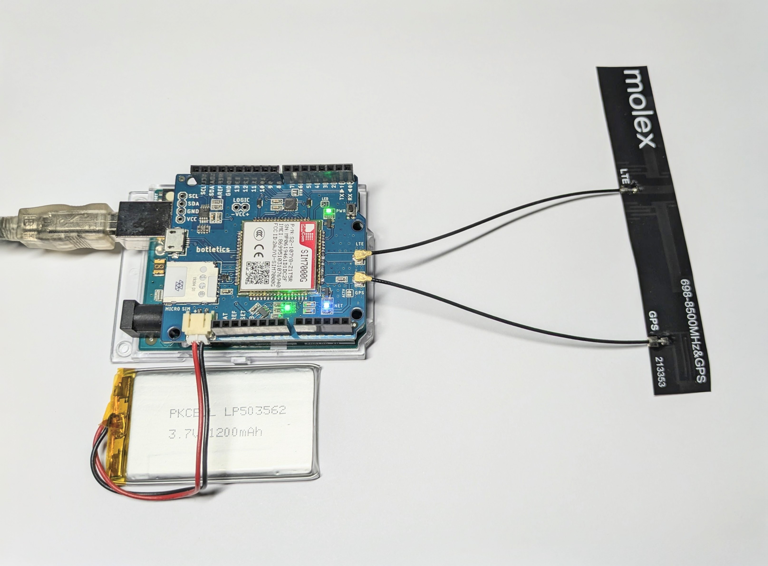
Media/SIM7000G Complete Setup.jpg
