botletics/SIM7000-LTE-Shield/Media/AT Command Test.PNG

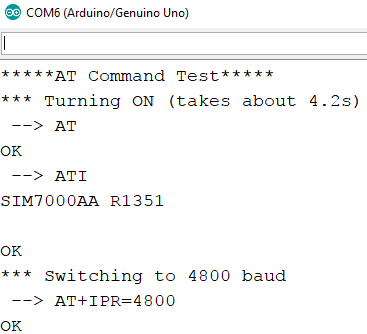
Media/AT Command Test.PNG
