botletics/SIM7000-LTE-Shield/Media/Hologram Event History.png

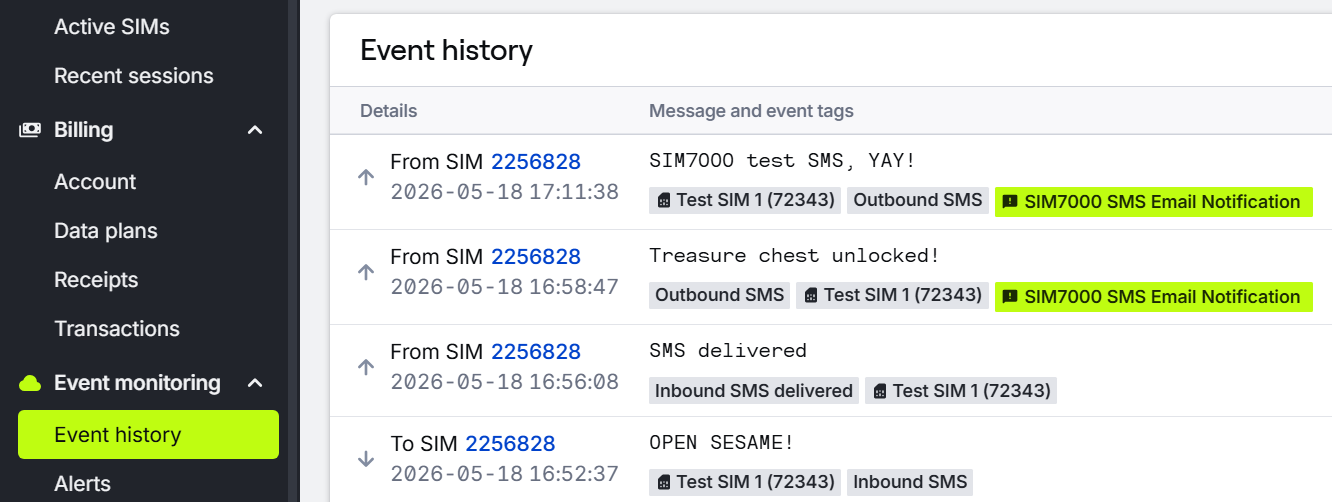
Media/Hologram Event History.png
